carloop/hardware/CarloopXL.v3/CarloopXL-v3-bottom.png

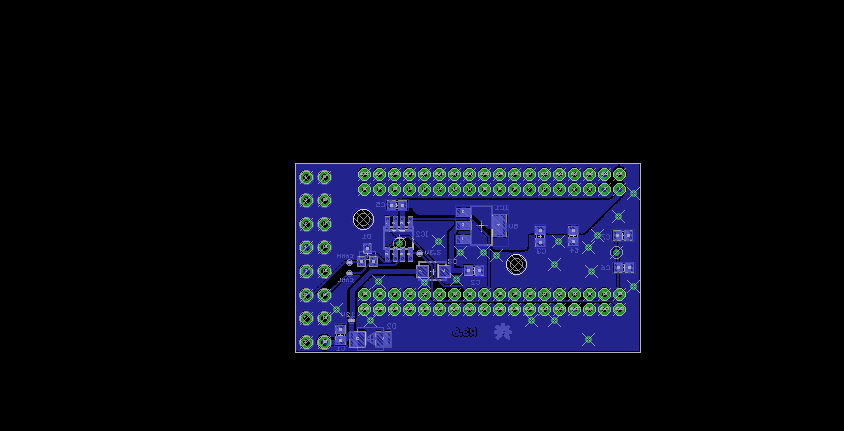
CarloopXL.v3/CarloopXL-v3-bottom.png
