carloop/hardware/CarloopXL.v3/CarloopXL-v3-top.png

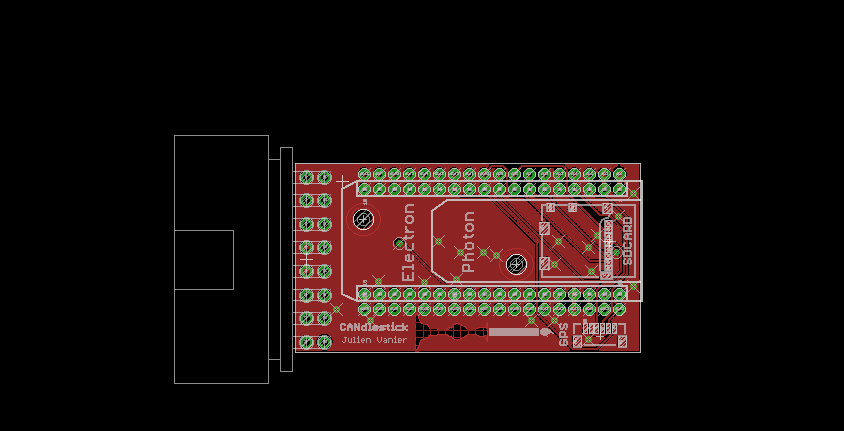
CarloopXL.v3/CarloopXL-v3-top.png
