carloop/hardware/images/detail-back.jpg

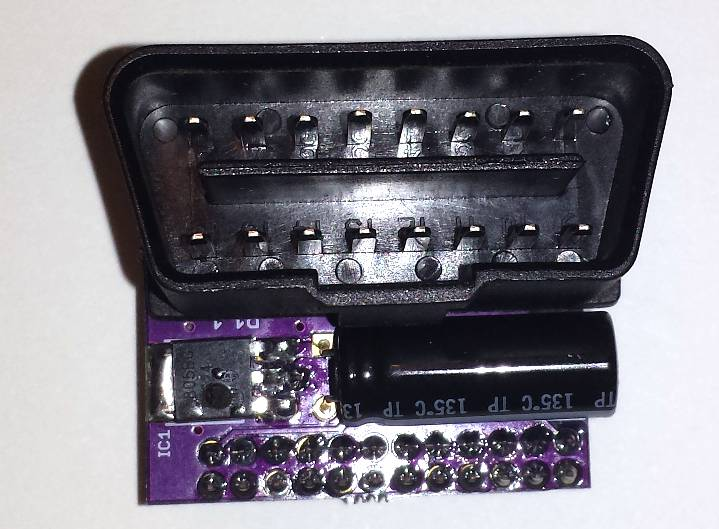
images/detail-back.jpg
