carloop/hardware/images/detail-electron.jpg

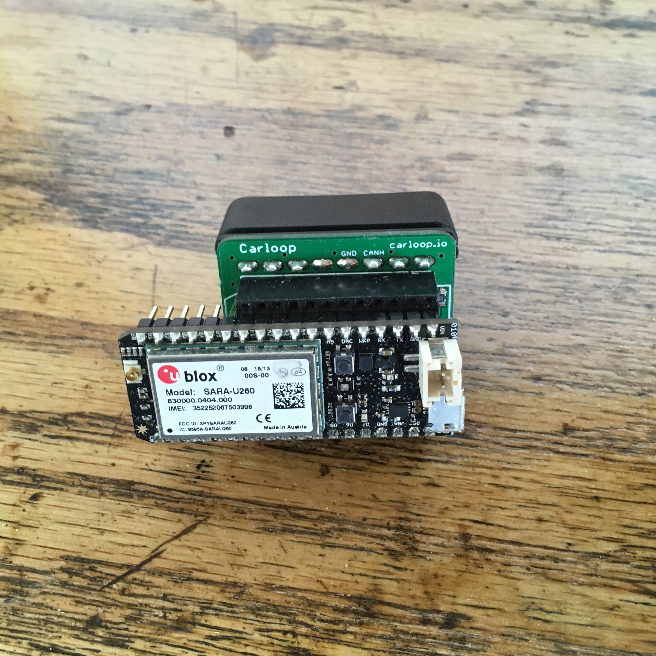
images/detail-electron.jpg
