carloop/hardware/images/detail-front.jpg

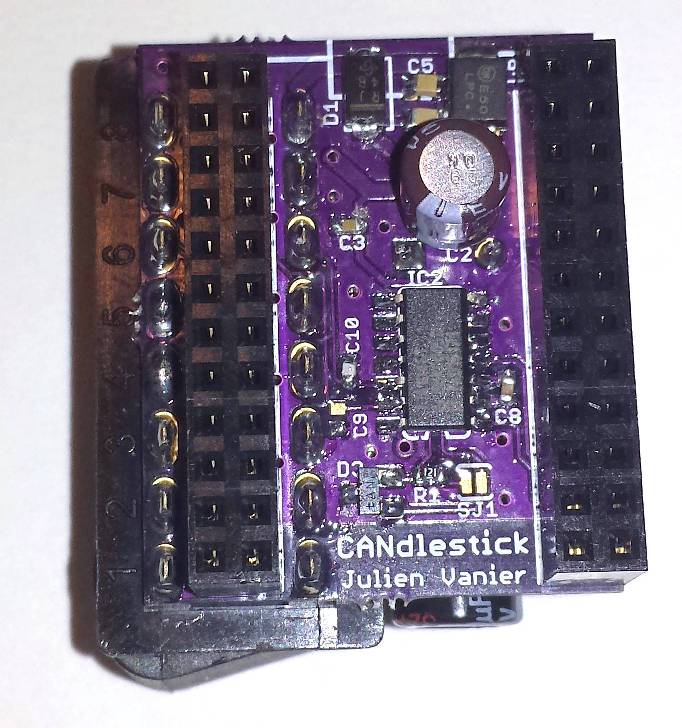
images/detail-front.jpg
