carloop/hardware/images/pcb-top.png

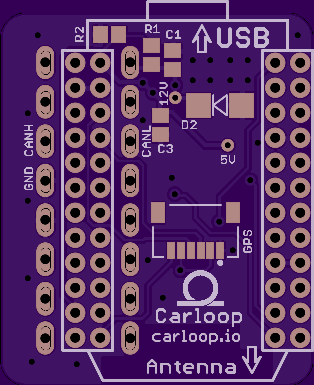
images/pcb-top.png
