carloop/hardware/images/photo.jpg

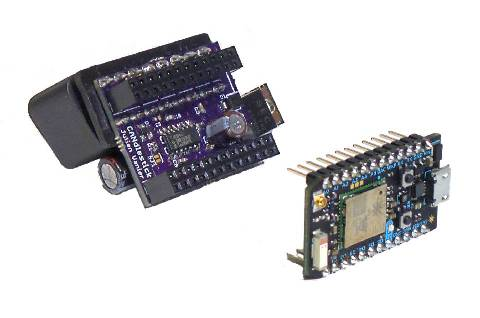
images/photo.jpg
