carloop/hardware/Power supply from STN1110.png

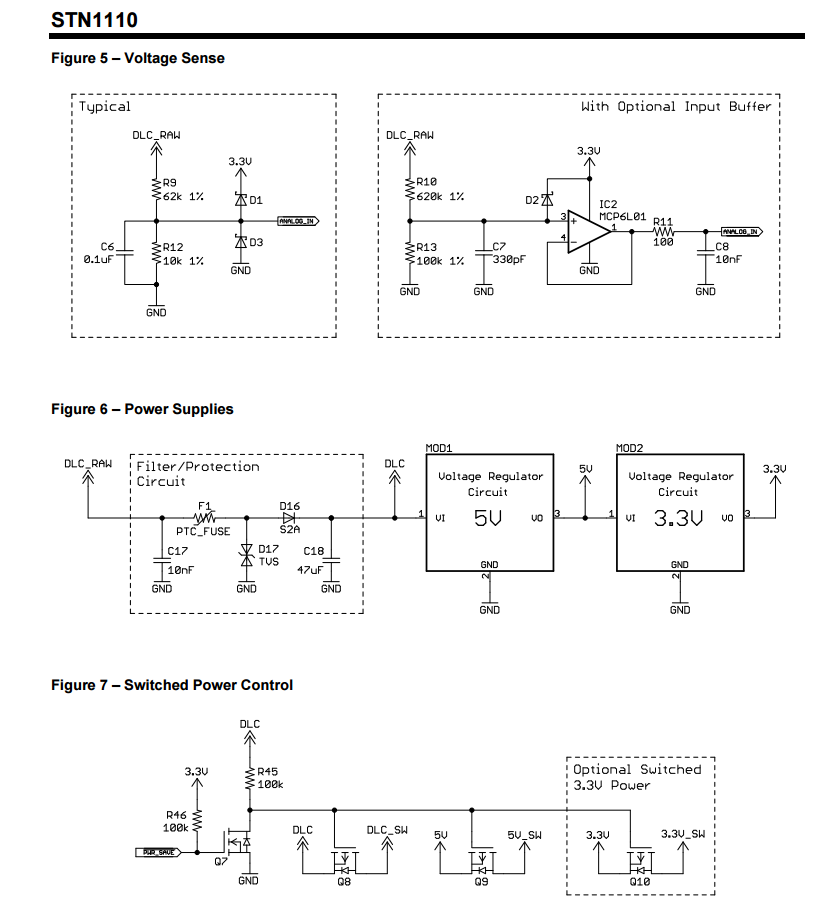
Power supply from STN1110.png
