carloop/hardware/CarloopXL.v3/CarloopXL-v3.0.pdf

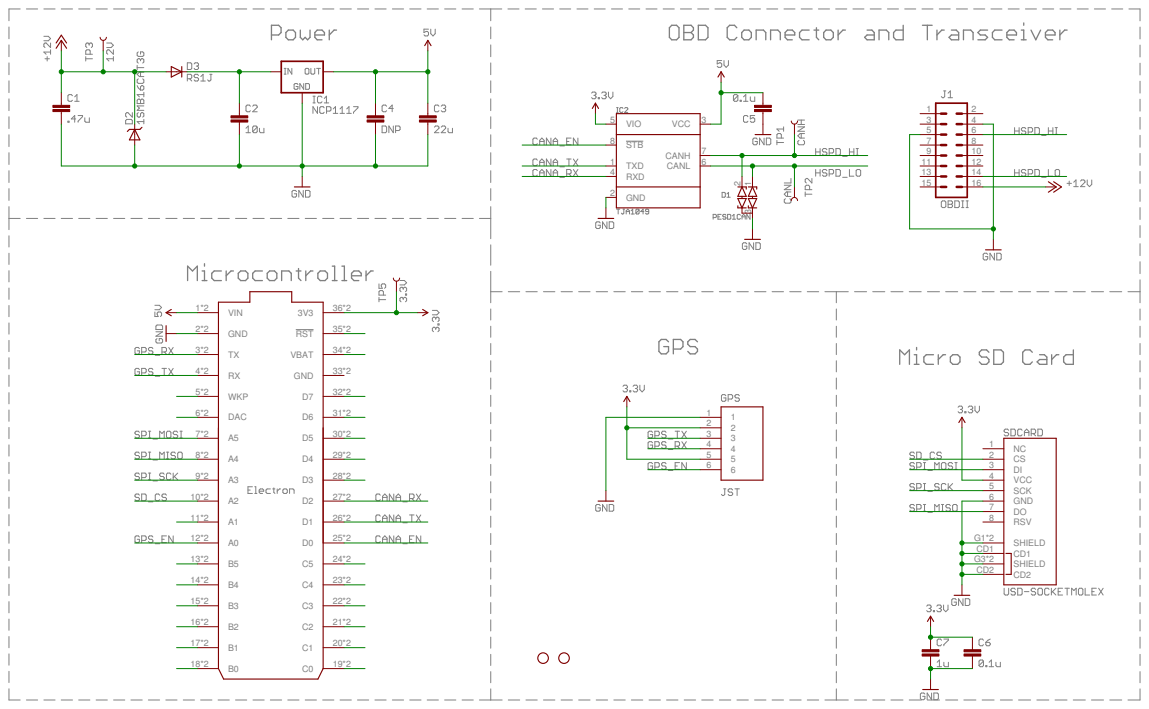
[picture p20: page 1]

21 3 1 2 3 4 5 6 7 8 9 10 11 12 13 14 15 16 STB 8 CANH 7 CANL 6 GND 2 RXD 4 TXD 1 VCC 3 VIO 5 1 1 2 2 3 3 4 4 5 5 6 6 CS 2 DI 3 GND 6 VCC 4 SCK 5 RSV 8 DO 7 NC 1 SHIELD G3*2 SHIELD G1*2 CD1 CD1 CD2 CD2 VIN 1*2 GND 2*2 TX 3*2 RX 4*2 WKP 5*2 DAC 6*2 A5 7*2 A4 8*2 A3 9*2 A2 10*2 A1 11*2 A0 12*2 3V3 36*2 RST 35*2 VBAT 34*2 GND 33*2 D7 32*2 D6 31*2 D5 30*2 D4 29*2 D3 28*2 D2 27*2 D1 26*2 D0 25*2 B5 13*2 B4 14*2 B3 15*2 B2 16*2 B1 17*2 B0 18*2 C5 24*2 C4 23*2 C3 22*2 C2 21*2 C1 20*2 C0 19*2
