carloop/hardware/Carloop.v2/Carloop-v2.3-pcb-top-docu.pdf

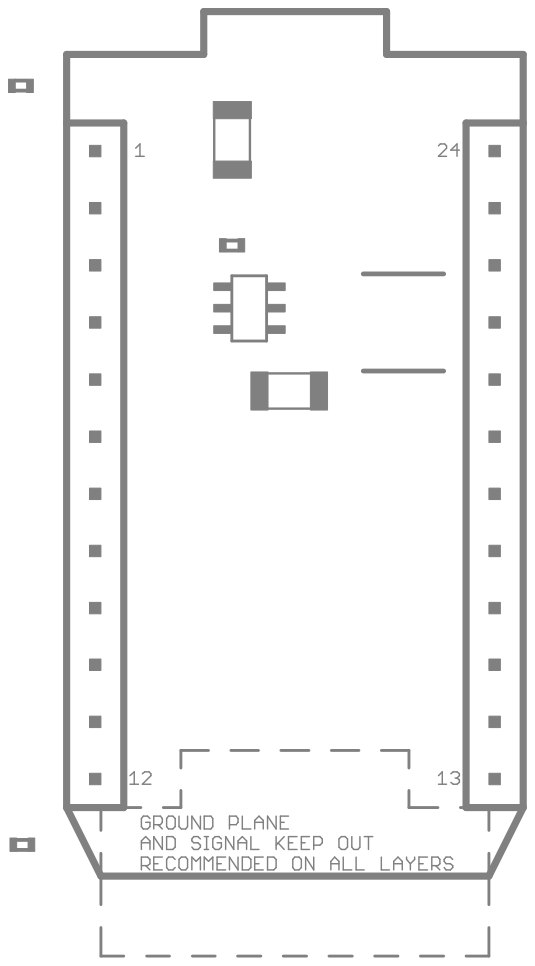
[picture p40: page 1]
