carloop/hardware/Carloop.v2/Carloop-v2.3-pcb-top.pdf

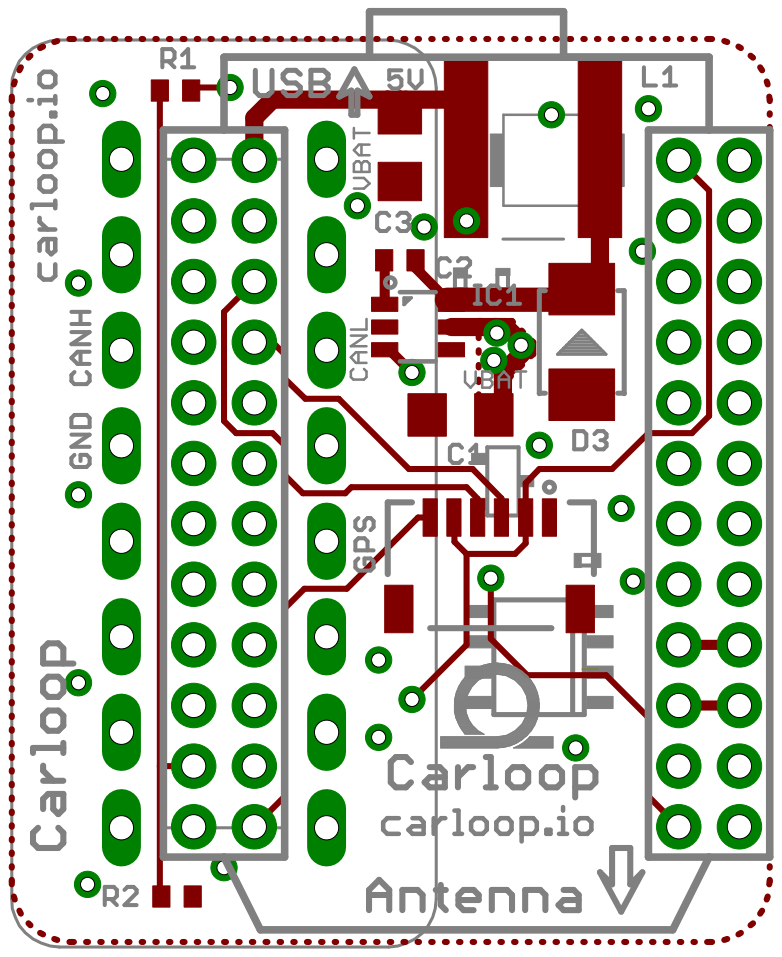
[picture p41: page 1]
