carloop/hardware/Carloop.v2/Carloop-v2.3-pcb-vias.pdf

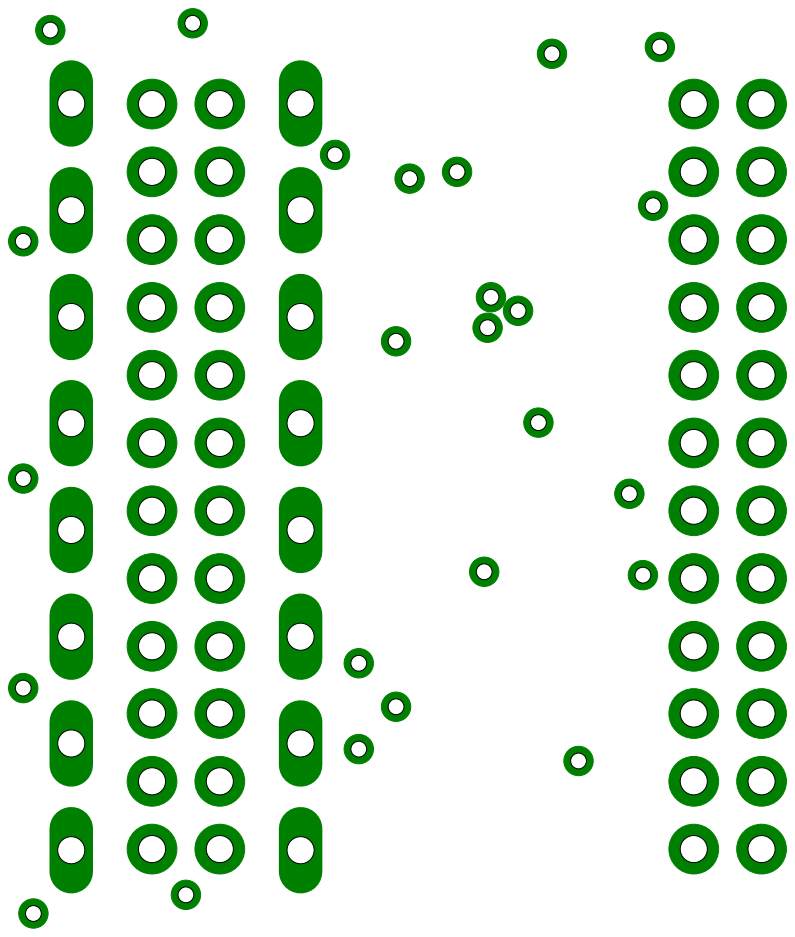
[picture p42: page 1]
