carloop/hardware/Carloop2.v3/Carloop2-v3.1.pdf

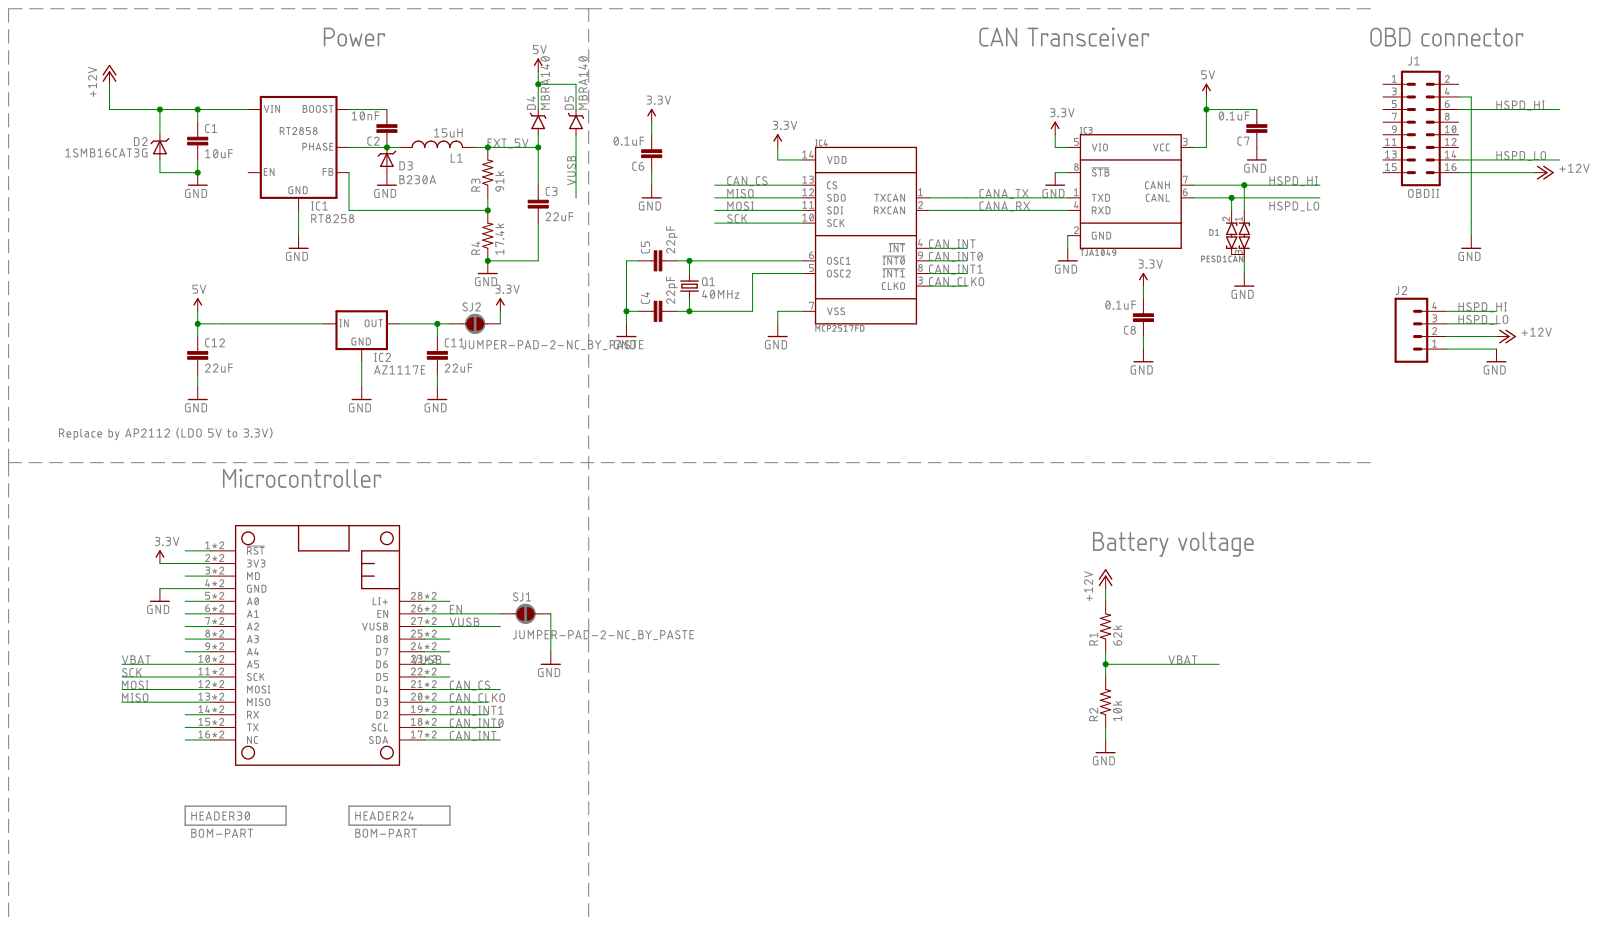
[picture p43: page 1]
