carloop/hardware/Carloop.v2/Carloop-v2.1-layout-bottom.pdf

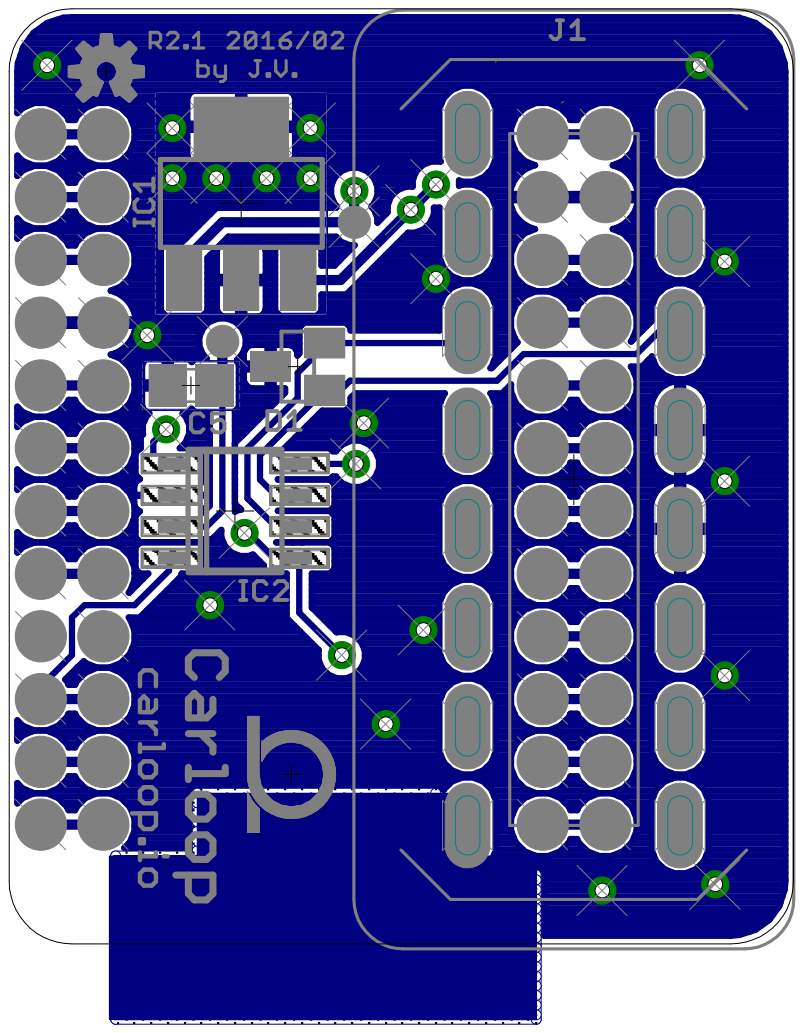
[picture p44: page 1]
