carloop/hardware/Carloop.v2/Carloop-v2.1-layout-top.pdf

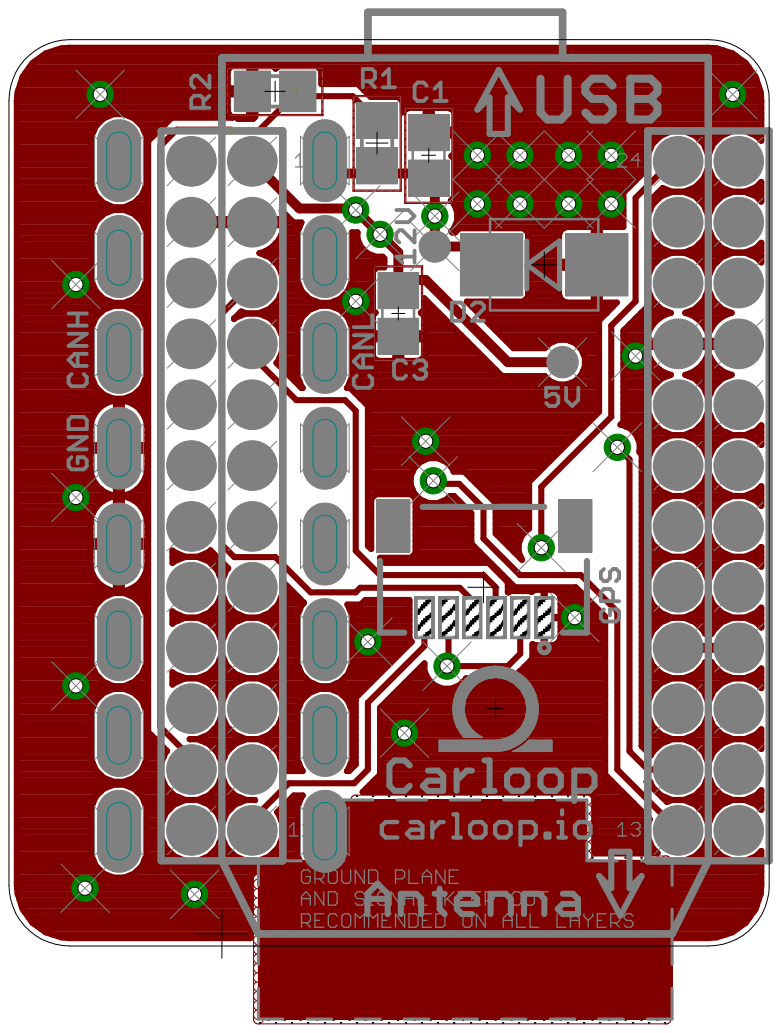
[picture p45: page 1]
